Krakenpine/Tomboi/midi_notes.cpp

float midi_notes[] = { 8.176,
8.662,
9.177,
9.723,
10.301,
10.913,
11.562,
12.250,
12.978,
13.750,
14.568,
15.434,
16.352,
17.324,
18.354,
19.445,
20.602,
21.827,
23.125,
24.500,
25.957,
27.500,
29.135,
30.868,
32.703,
34.648,
36.708,
38.891,
41.203,
43.654,
46.249,
48.999,
51.913,
55.000,
58.270,
61.735,
65.406,
69.296,
73.416,
77.782,
82.407,
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
